zhbi98/LinuxDK/Docs/20230415173712.jpg

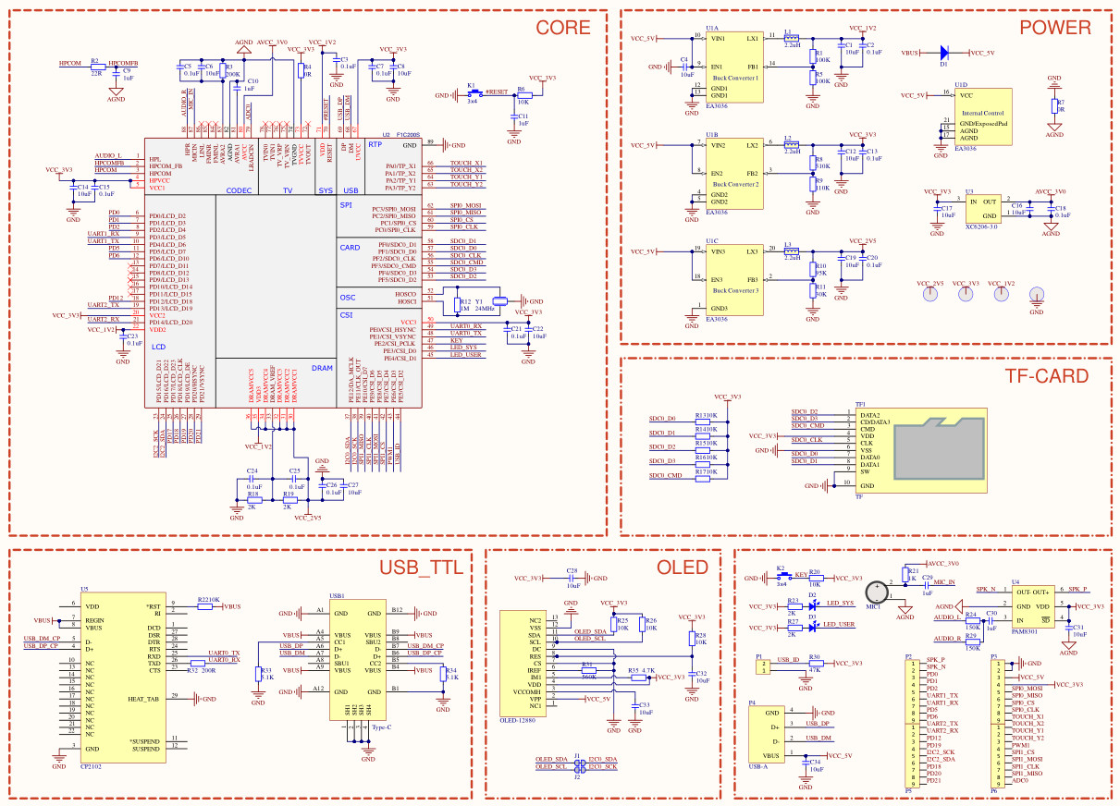
Docs/20230415173712.jpg
