zhbi98/LinuxDK/Docs/20230415173713.png

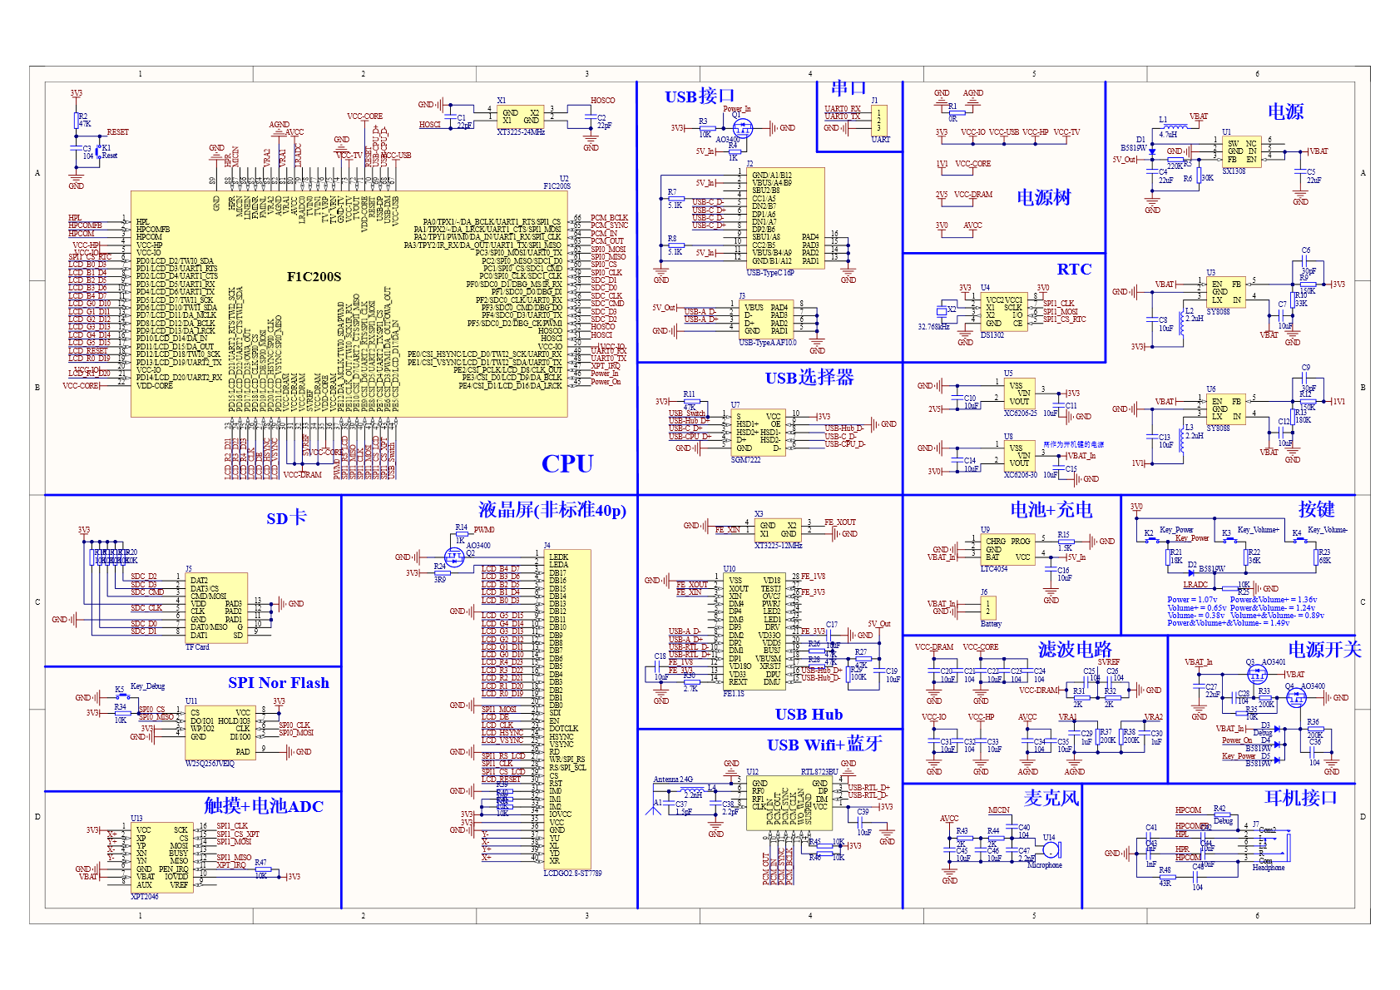
Docs/20230415173713.png
